mlehmann76/dispstepper/hardware/reva/pdf/reva.pdf

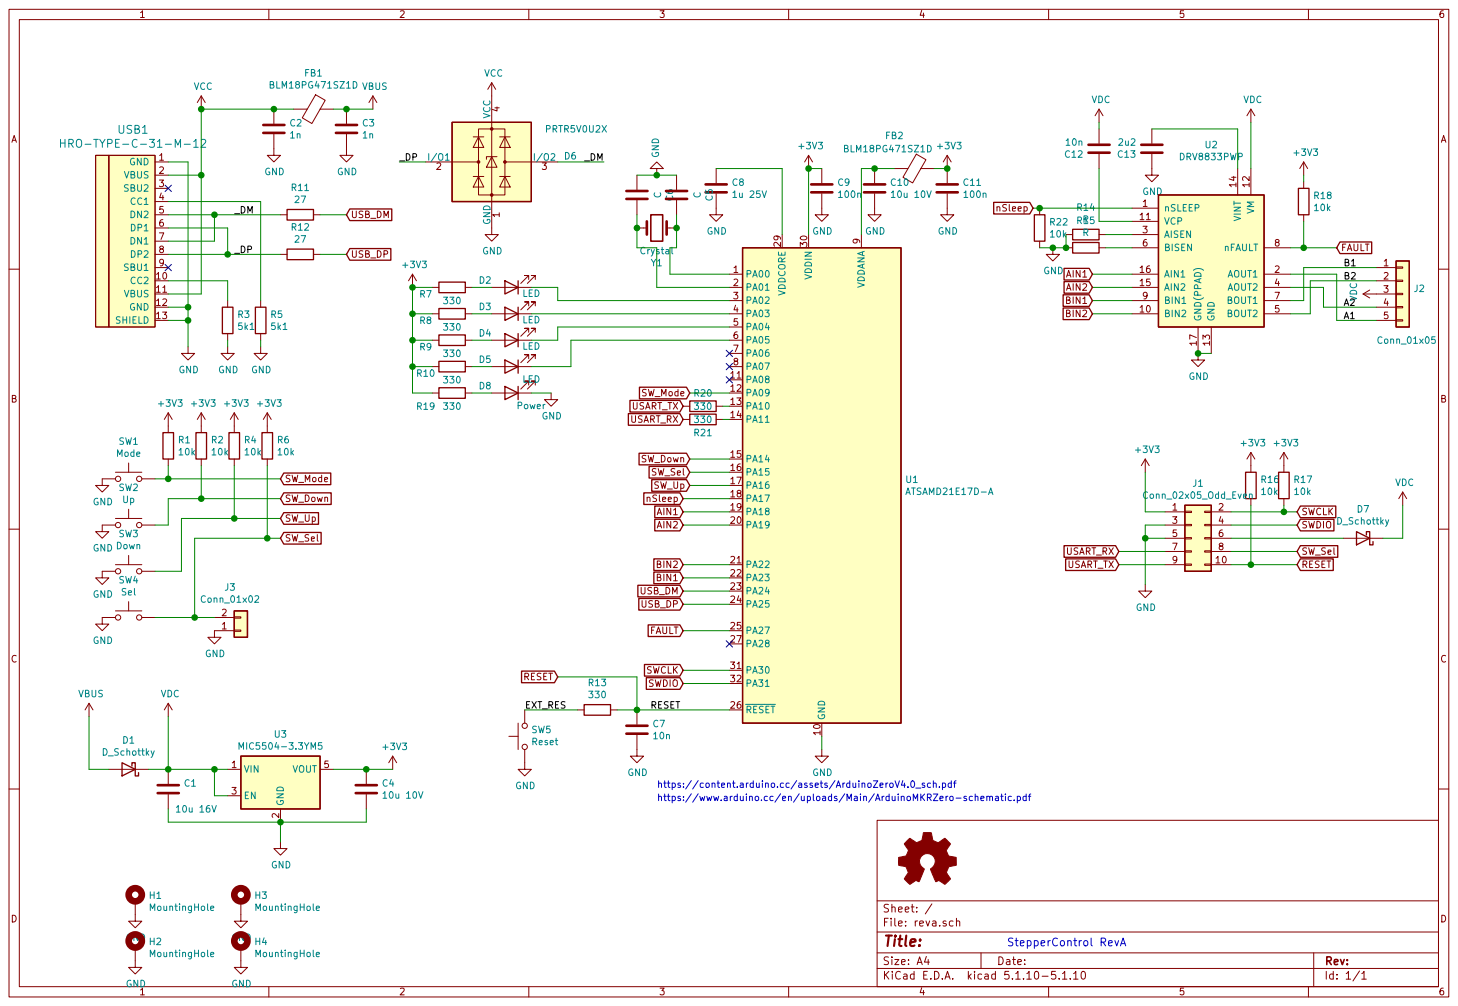
[picture p3: page 1]

https://content.arduino.cc/assets/ArduinoZeroV4.0_sch.pdf
https://www.arduino.cc/en/uploads/Main/ArduinoMKRZero-schematic.pdf

Id: 1/1 Title: File: reva.sch Sheet: /
