mlehmann76/dispstepper/firmware/include/stepper.h

#ifndef __STEPPER_H_
#define __STEPPER_H_

#include <stdint.h>
#include <stdbool.h>

#define STEPS 8


class stepCtrl {
  public:
    enum dir_t { CW, CCW };

    stepCtrl(uint32_t stepsPerTurn, float timerFreq);
    void cw(float speed, uint32_t steps);
    void ccw(float speed, uint32_t steps);
    void func(uint16_t timerVal);
    bool isRunning() const { return _steps > 0 ? true : false; }
    dir_t dir() const {return _dir;}

  private:
    float _timerFreq;
    uint32_t _stepsPerTurn;
    dir_t _dir;
    uint32_t _steps;
    uint16_t _lastTimerVal;
    uint16_t _timerValPerStep;
    uint8_t _stepIndex;
};

#endif // !__STEPPER_H_
