mlehmann76/dispstepper/firmware/include/conf_board.h

/**
 * \file
 *
 * \brief User board configuration template
 *
 */
/*
 * Support and FAQ: visit <a href="https://www.microchip.com/support/">Microchip Support</a>
 */

#ifndef CONF_BOARD_H
#define CONF_BOARD_H

#include <atmel_start_pins.h>

#endif // CONF_BOARD_H
